fgcoca/Granabot-badge/Images/Botton.png

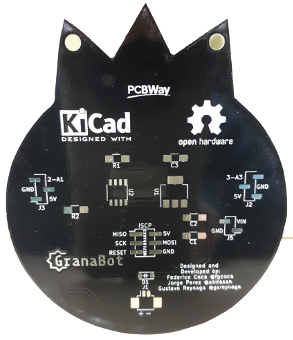
Images/Botton.png
