fgcoca/Granabot-badge/Images/Sorteo.png

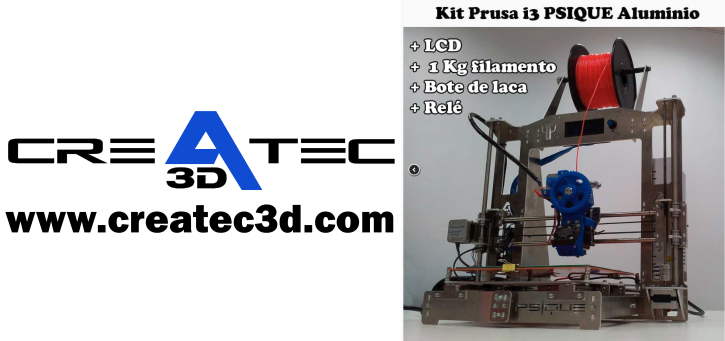
Images/Sorteo.png
