fgcoca/Granabot-badge/Kit/Programacion/Images/01_1Detalle-cable-ICSP.jpg

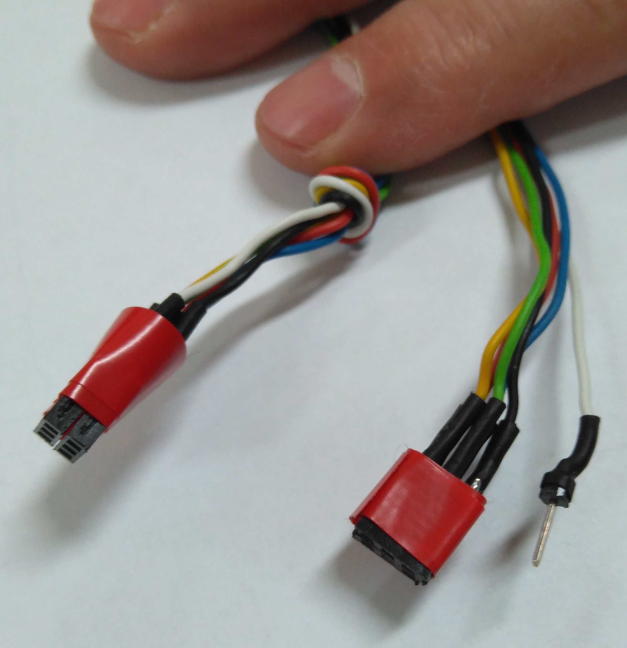
Kit/Programacion/Images/01_1Detalle-cable-ICSP.jpg
