fgcoca/Granabot-badge/Kit/Programacion/Images/IMG_20180417_125527_070.jpg

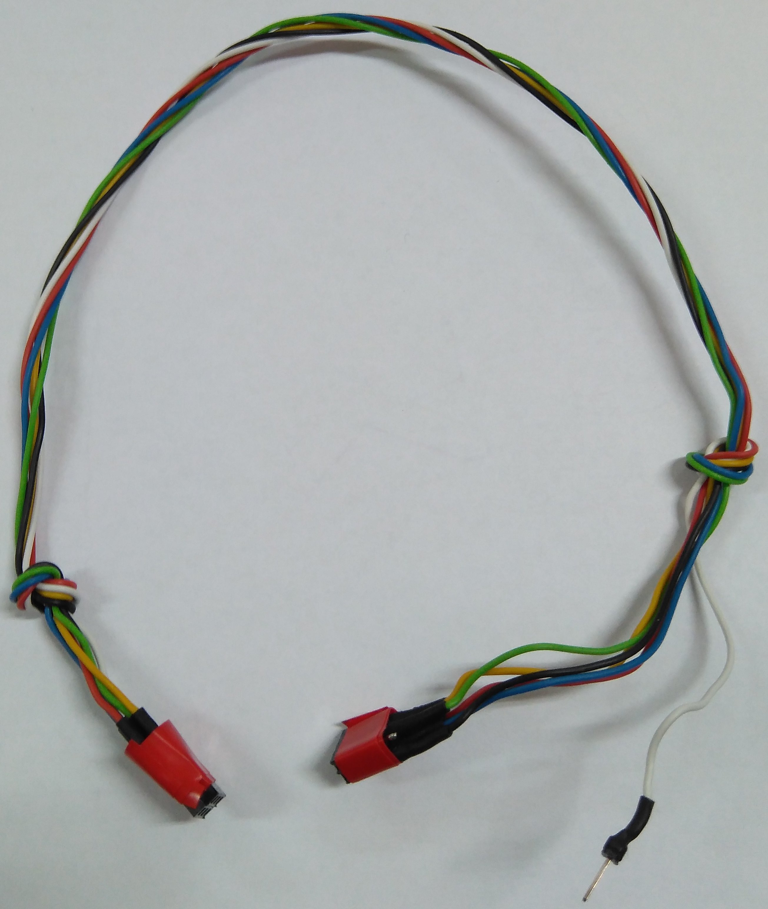
Kit/Programacion/Images/IMG_20180417_125527_070.jpg
