fgcoca/Granabot-badge/Kit/Programacion/Images/IMG_20180419_132812_424.jpg

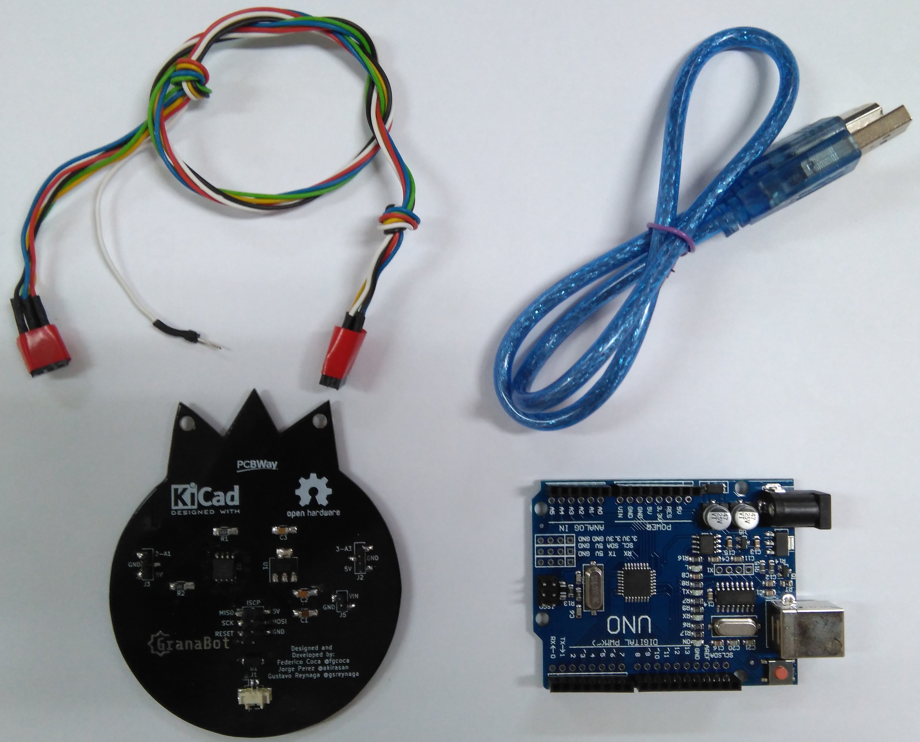
Kit/Programacion/Images/IMG_20180419_132812_424.jpg
