fgcoca/Granabot-badge/Kit/Programacion/Images/IMG_20180419_132953_211.jpg

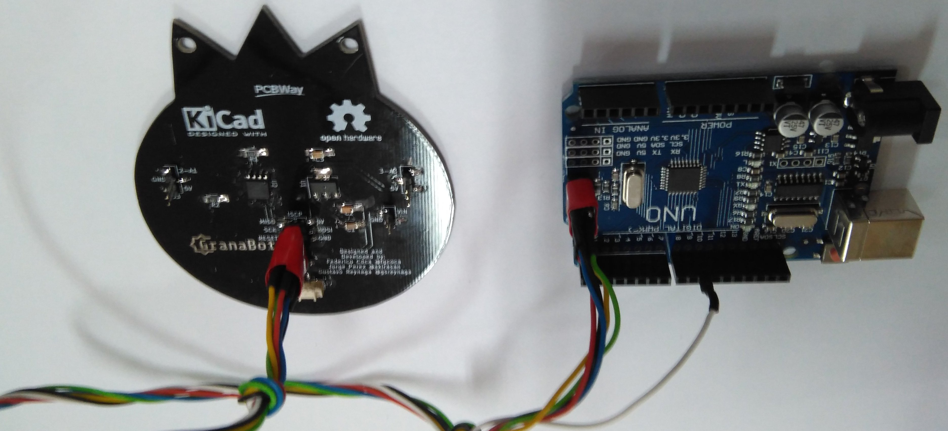
Kit/Programacion/Images/IMG_20180419_132953_211.jpg
