fgcoca/Granabot-badge/Kit/Programando/Images/01Cable_ICSP-Zocalo.jpg

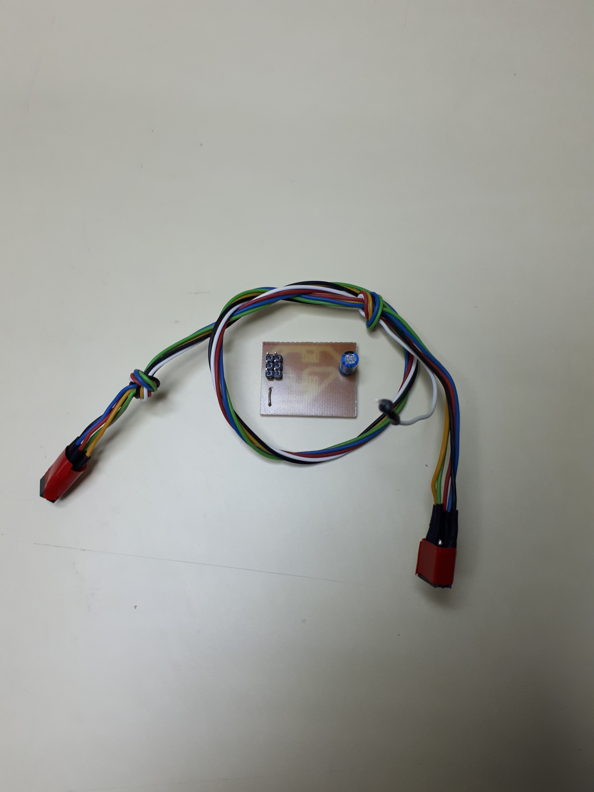
Kit/Programando/Images/01Cable_ICSP-Zocalo.jpg
