fgcoca/Granabot-badge/Kit/Programando/Images/02Zocalo-con-Marco-guia.jpg

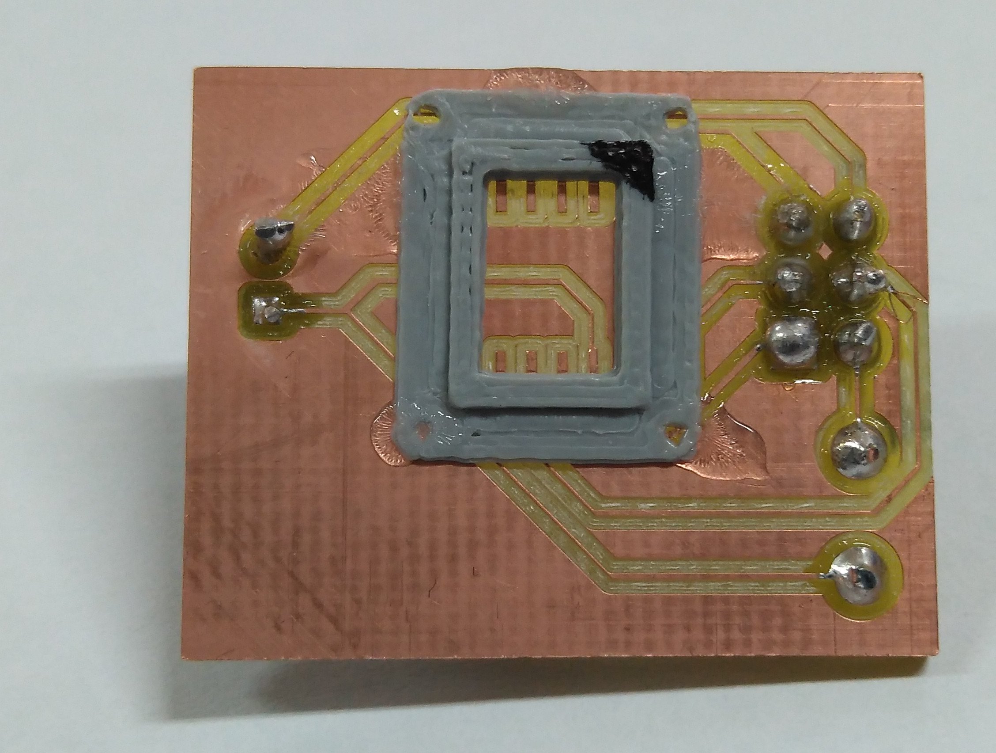
Kit/Programando/Images/02Zocalo-con-Marco-guia.jpg
