fgcoca/Granabot-badge/Kit/Programando/Images/04Conex-Arduino.jpg

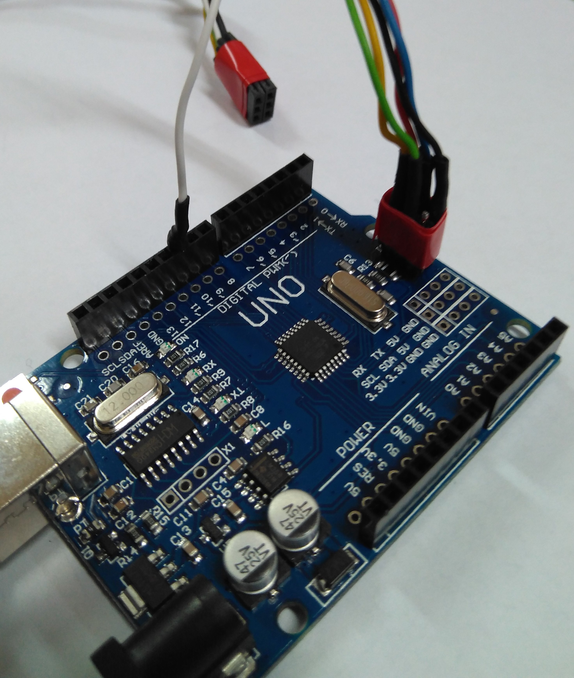
Kit/Programando/Images/04Conex-Arduino.jpg
