fgcoca/Granabot-badge/Kit/Programando/Images/05Conex-Zocalo.jpg

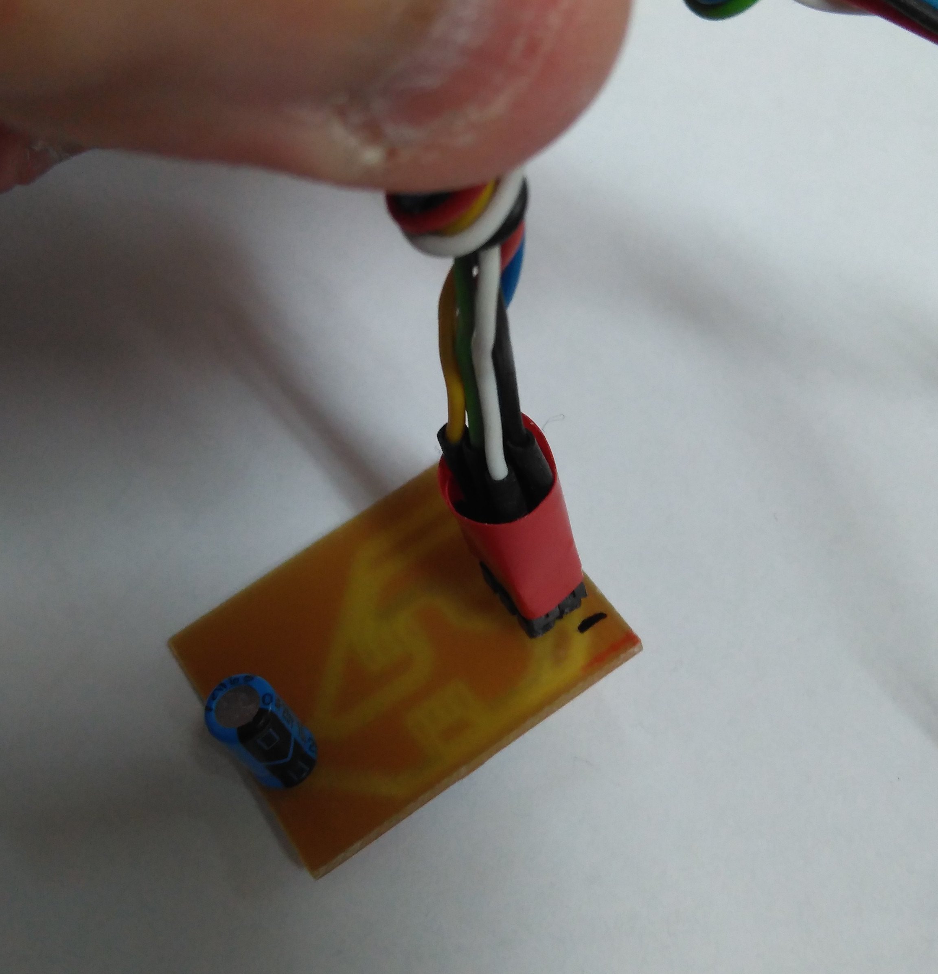
Kit/Programando/Images/05Conex-Zocalo.jpg
