fgcoca/Granabot-badge/Kit/Programando/Images/06Conexionado.jpg

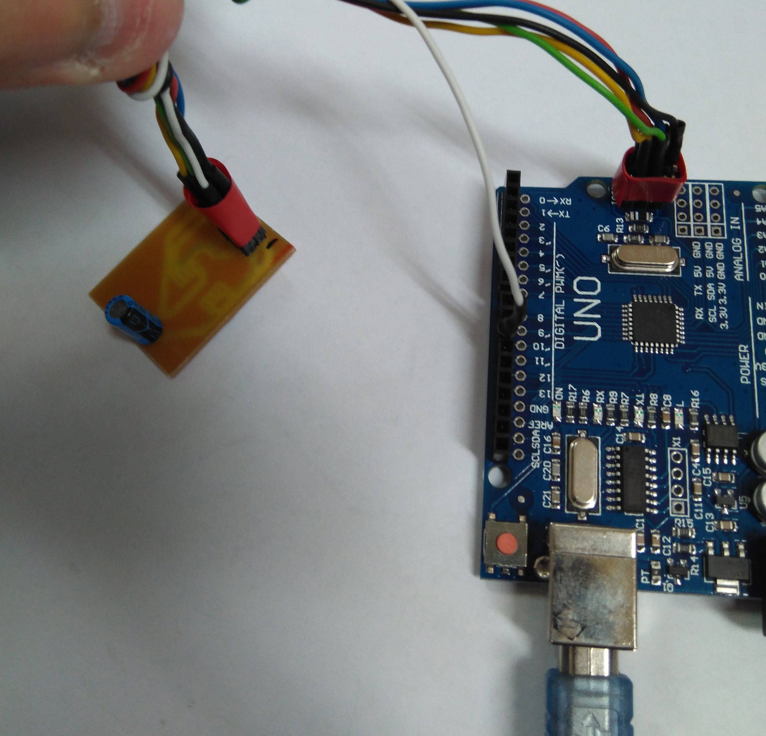
Kit/Programando/Images/06Conexionado.jpg
