fgcoca/Granabot-badge/Kit/Programando/Images/07Colocacion-ATTiny.jpg

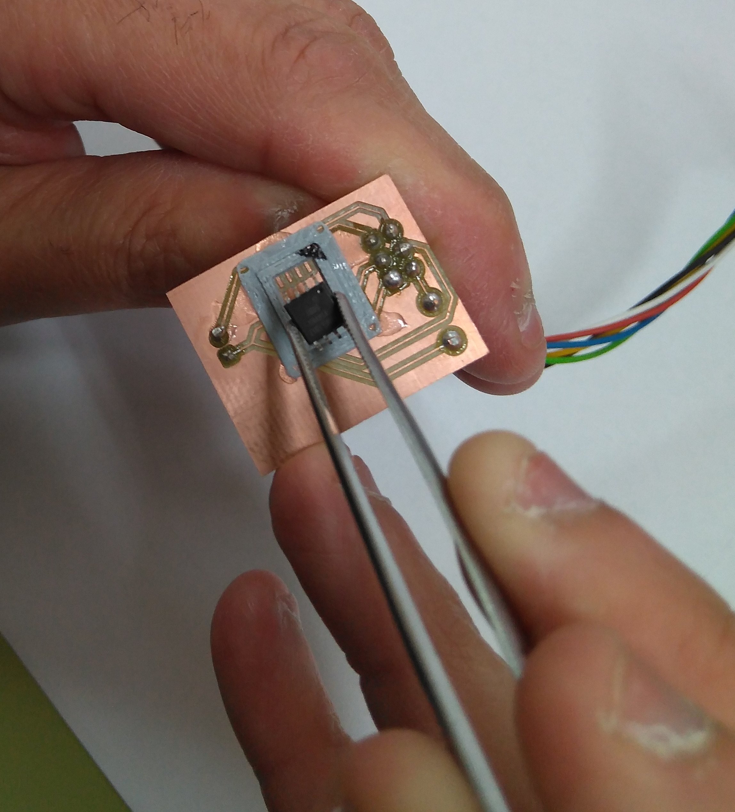
Kit/Programando/Images/07Colocacion-ATTiny.jpg
