fgcoca/Granabot-badge/Kit/Programando/Images/08ATTiny-colocado.jpg

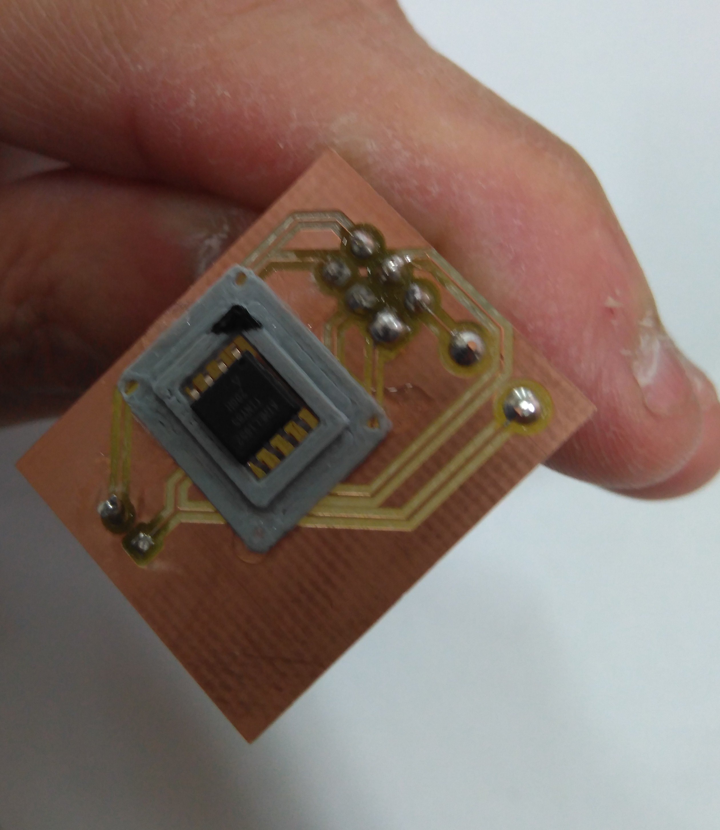
Kit/Programando/Images/08ATTiny-colocado.jpg
