fgcoca/Granabot-badge/Kit/Programando/Images/11Accionamiento-pinza.jpg

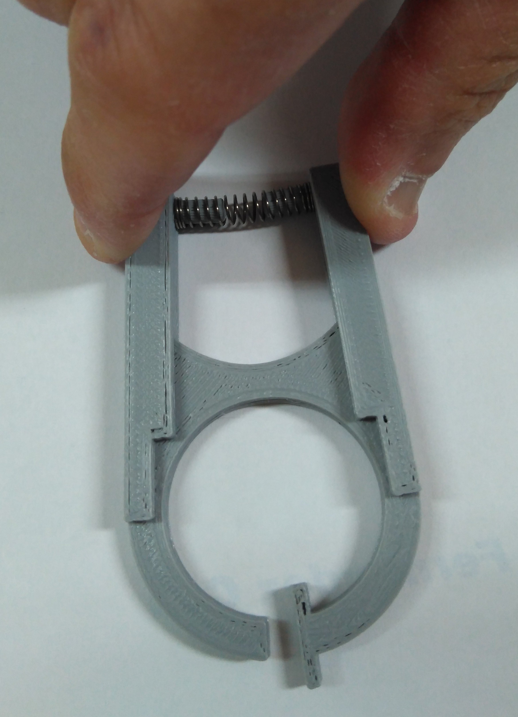
Kit/Programando/Images/11Accionamiento-pinza.jpg
