fgcoca/Granabot-badge/Pegatinas-Caja/PegatinaMezcla.svg.png

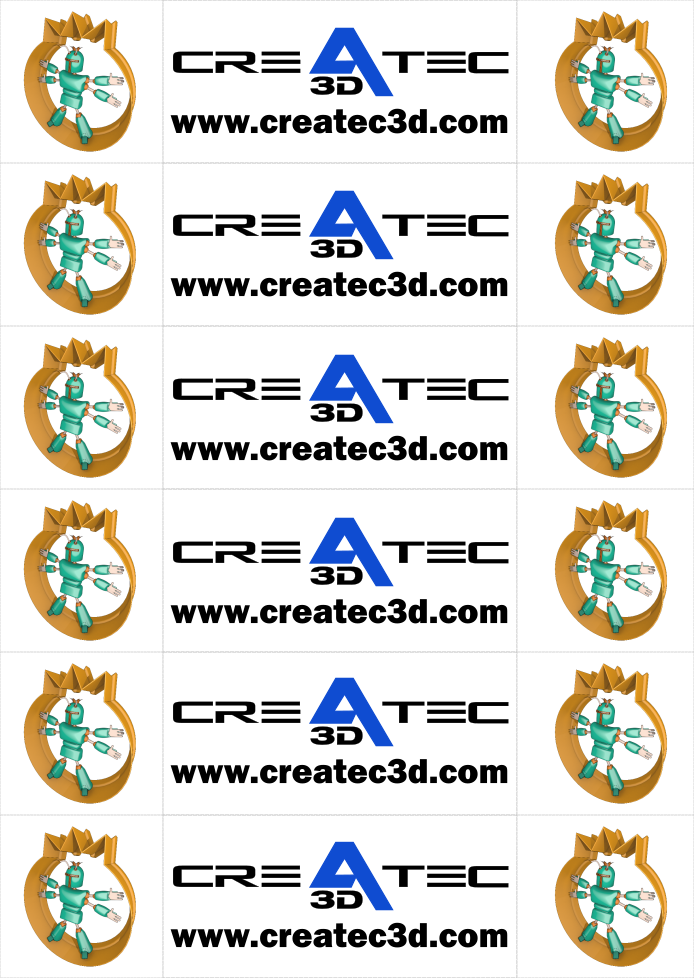
Pegatinas-Caja/PegatinaMezcla.svg.png
