fgcoca/Granabot-badge/Pegatinas-Caja/PegatinaTapa.svg.png

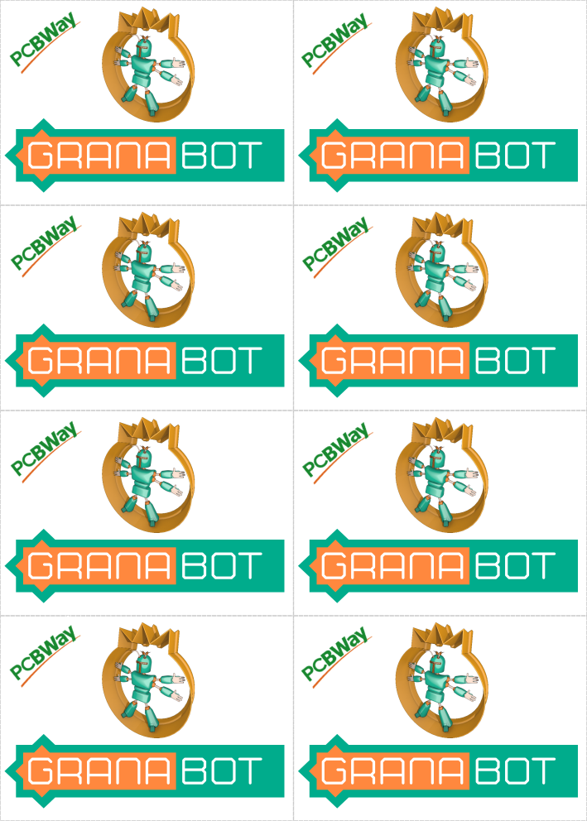
Pegatinas-Caja/PegatinaTapa.svg.png
