fgcoca/Granabot-badge/Kit/BOM/BOM.png

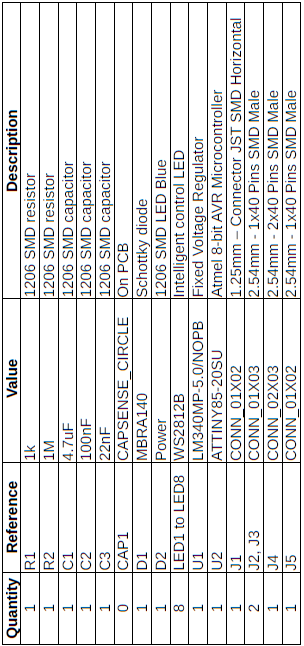
Kit/BOM/BOM.png
